FreyaAmiga/tf520/rtl/tf520.v

`timescale 1ns / 1ps
/* 
 
 This file is part of the Terrible Fire Amiga 520 Accelerator.
 
 Copyright (c) 2016, Stephen J. Leary <stephen@terriblefire.com>
 
 All rights reserved.

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
*/

module tf520(
		   input 	 CLKCPU,
           input 	 CLK7M,

           input 	 BG20,
           input 	 AS20,
           input 	 DS20,
           input 	 RW20,
           output 	 RW00,

           
           input [2:0] 	 FC,
           input [1:0] 	 SIZ,

           input         A0,   
           input [19:16] A,

           input 	 BGACK,
           input 	 VPA,
           input 	 DTACK,

           output 	 BG,
           output 	 LDS,
           output 	 UDS,
           output 	 VMA,
           output reg E,
           output 	 AS,
           output    BERR,
        
           output 	 DSACK1,
           output 	 AVEC
       );

wire DS20DLY;
wire AS20DLY;

reg SYSDSACK1 = 1'b1;
reg RW20DLY = 1'b1;
reg CLK7MB2 = 1'b1;
reg BGACKD1 = 1'b1;
reg BGACKD2 = 1'b1;

reg [3:0] Q = 'hF;

reg VMA_SYNC = 1'b1;

initial begin 

	E = 'b0;
	
end

reg  DTQUAL = 1'b0;

wire DTRIG;
wire DTRIG_SYNC;

wire CPUSPACE = &FC;

wire CPCS = CPUSPACE & ({A[19:16]} === {4'b0010});
wire BKPT = CPUSPACE & ({A[19:16]} === {4'b0000});
wire IACK = CPUSPACE & ({A[19:16]} === {4'b1111});
wire DTACKPRELIM = CLK7M | CLK7MB2;

FDCP #(.INIT(1'b1)) 
	AS20DLY_FF (
		.Q(AS20DLY), // Data output
		.C(CLK7M), // Clock input
		.CLR(1'b0), // Asynchronous clear input
		.D(AS20), // Data input
		.PRE(AS20) // Asynchronous set input
);

FDCP #(.INIT(1'b1)) 
	DS20DLY_FF (
		.Q(DS20DLY), // Data output
		.C(CLK7M), // Clock input
		.CLR(1'b0), // Asynchronous clear input
		.D(DS20), // Data input
		.PRE(DS20) // Asynchronous set input
);

FDCP #(.INIT(1'b1)) 
	DTTRIG1_FF (
		.Q(DSACK1INT), // Data output
		.C(~DTRIG), // Clock input
		.CLR(1'b0), // Asynchronous clear input
		.D(AS), // Data input
		.PRE(AS) // Asynchronous set input
);

always @(posedge CLKCPU) begin 

	SYSDSACK1 <= DSACK1INT | CPCS;

end

always @(posedge CLK7M) begin

	 DTQUAL 	<= AS20DLY;
	 RW20DLY <= RW20;
     
    BGACKD1 <= BGACK;
    BGACKD2 <= BGACKD1;
    
    // 7Mhz Clock divided by 2
    CLK7MB2 <= ~CLK7MB2;
    
   if (Q == 'd9) begin

      VMA_SYNC <= 1'b1;
      Q <= 'd0;

   end else begin

      Q <= Q + 'd1;

      if (Q == 'd4) begin
	 E <= 'b1;       
      end

      if (Q == 'd8) begin
	 E <= 'b0;
      end

      if (Q == 'd2) begin

         VMA_SYNC <= VPA | CPUSPACE;
		 
      end 
      
   end
 
end
   
//wire HIGHZ = BG20 | //(BG20 & (AS20DLY | AS20)) | CPUSPACE;
wire HIGHZ = (BG20 & (AS20DLY | AS20)) | CPUSPACE;
wire AS_INT = AS20DLY | AS20;
wire UDS_INT = DS20 | DS20DLY | A0;
wire LDS_INT = DS20 | DS20DLY | ({A0, SIZ[1:0]} == 3'b001);  
wire VMA_INT = VMA_SYNC;  
 
assign RW00 = RW20DLY | RW20;      
assign AS = AS_INT;   
assign UDS =  UDS_INT;
assign LDS =   LDS_INT;
assign VMA =  VMA_INT;

assign DTRIG_SYNC = ~Q[3] | VMA_SYNC;
assign DTRIG = (DTACK | DTQUAL) & DTRIG_SYNC;
assign DSACK1 = (AS20DLY |  AS20 | SYSDSACK1);

assign BG = BG20;
assign AVEC = ~IACK | VPA;
assign BERR = ~CPCS;
      
endmodule
